RealSynarix/Cobalt-X-Zero/docs/media/images/reference/2.jpg

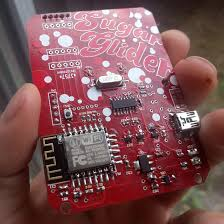
docs/media/images/reference/2.jpg
