RealSynarix/Cobalt-X-Zero/docs/media/images/reference/4.jpg

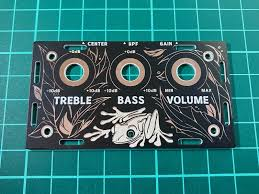
docs/media/images/reference/4.jpg
