RealSynarix/Cobalt-X-Zero/docs/media/images/reference/My-Schem.png

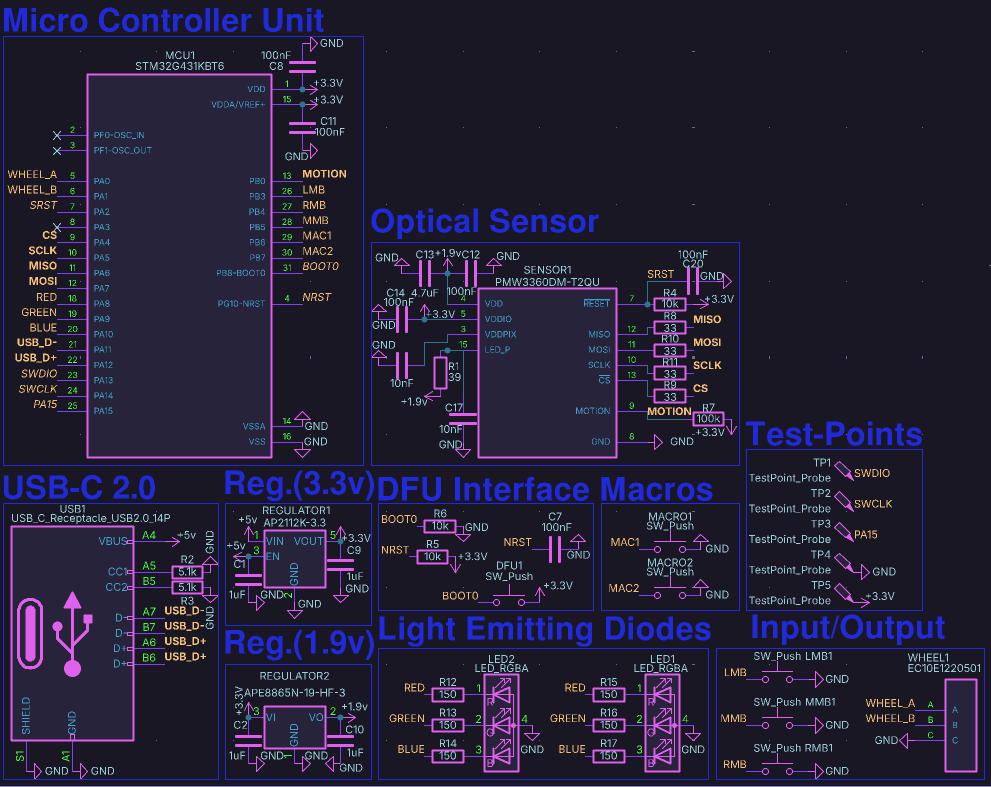
docs/media/images/reference/My-Schem.png
