RealSynarix/Cobalt-X-Zero/docs/media/images/reference/My-Sensor-Block.png

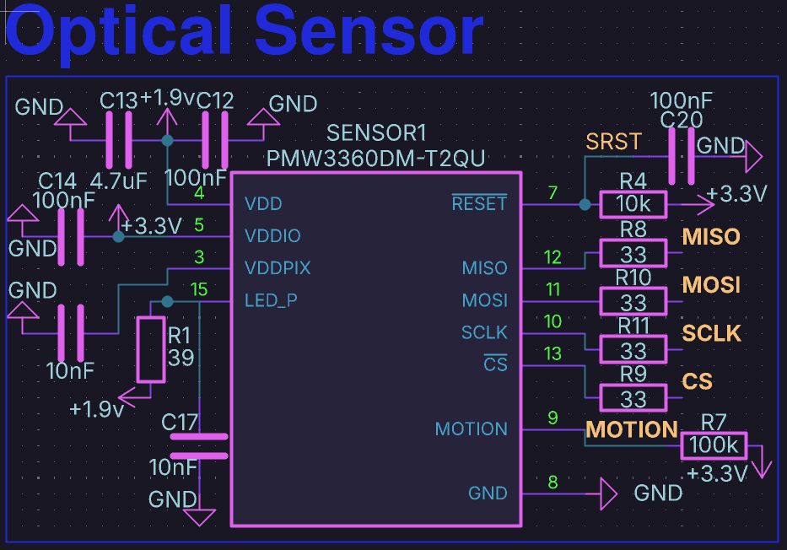
docs/media/images/reference/My-Sensor-Block.png
