RealSynarix/Cobalt-X-Zero/docs/media/images/reference/Proto1.png

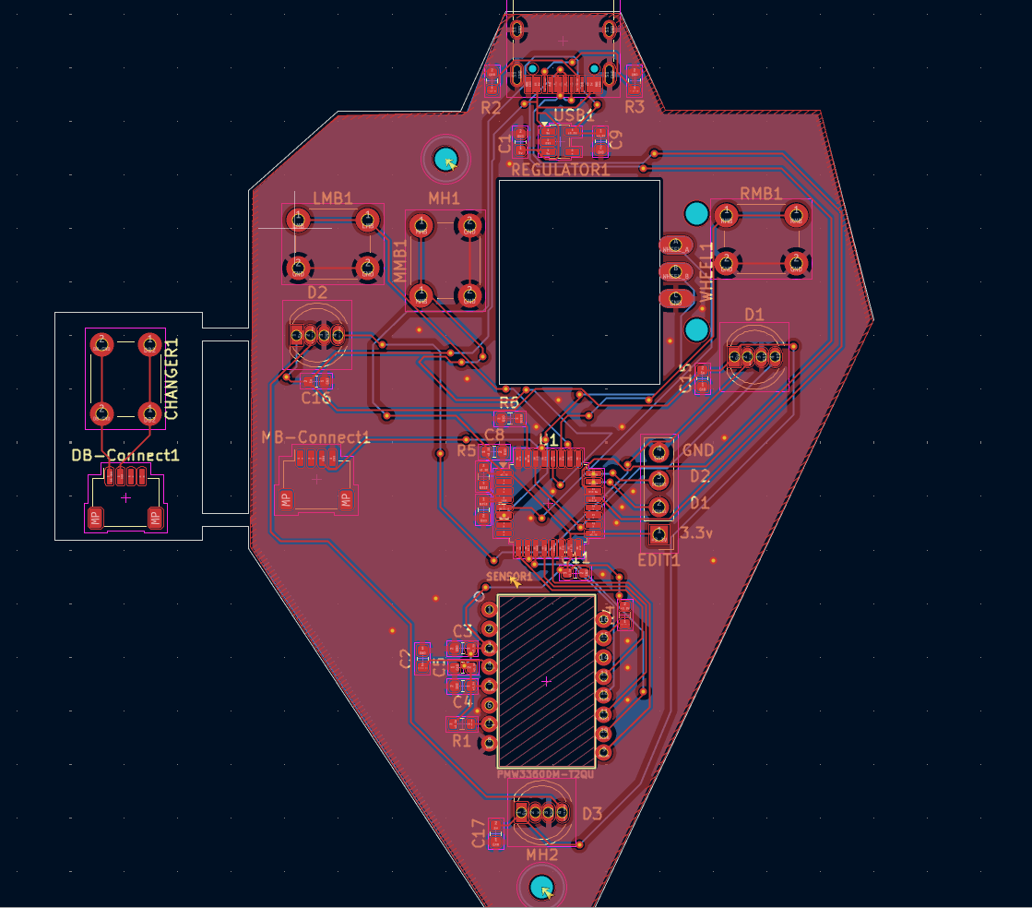
docs/media/images/reference/Proto1.png
