RealSynarix/Cobalt-X-Zero/docs/media/images/reference/Proto2-SCRAPPED.png

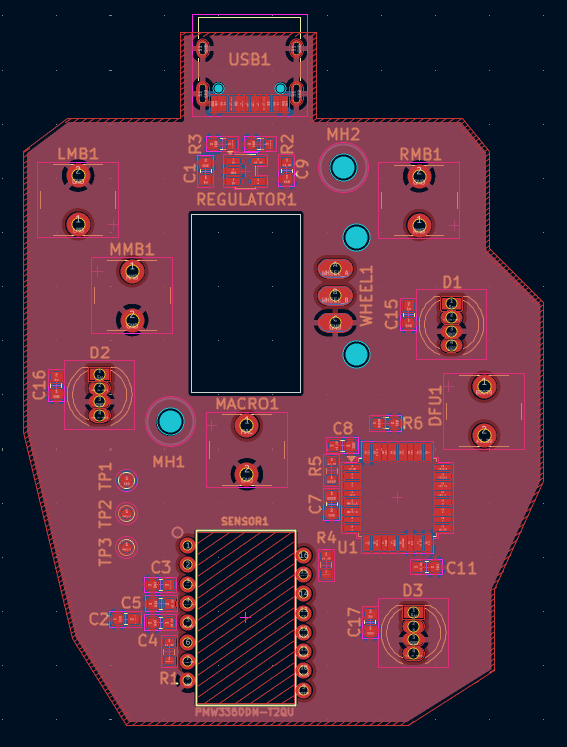
docs/media/images/reference/Proto2-SCRAPPED.png
