RealSynarix/Cobalt-X-Zero/docs/media/images/reference/working-ref.webp

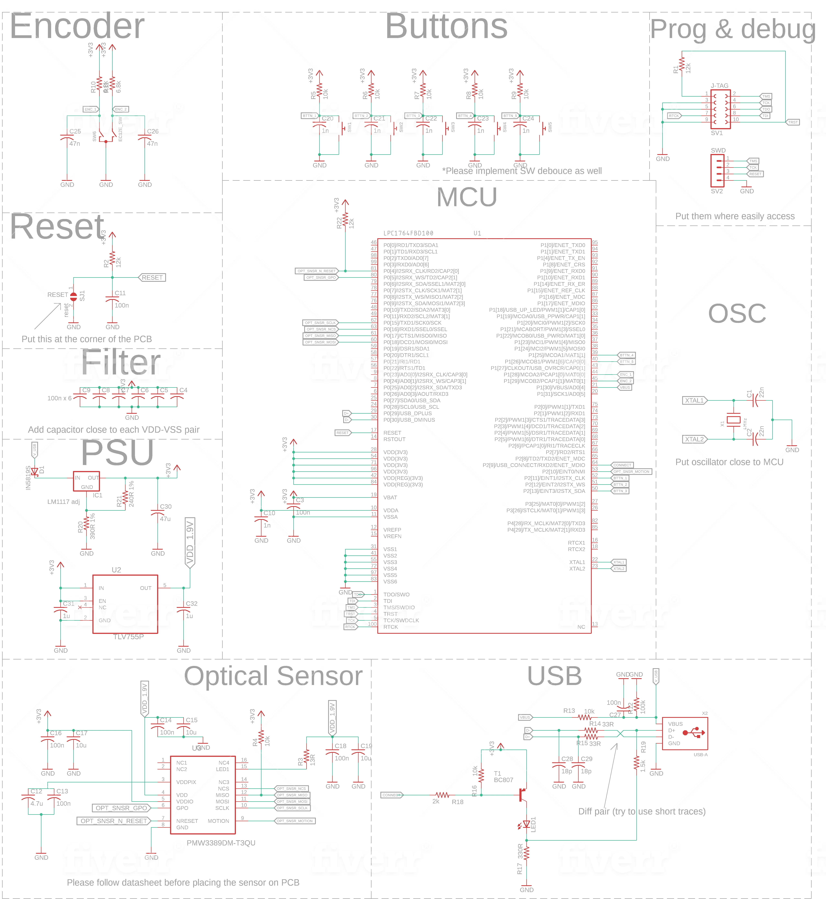
docs/media/images/reference/working-ref.webp
