RealSynarix/Cobalt-X-Zero/firmware/source/src/Sensor-Module/srom_04.h

#pragma once
#include <stdint.h>
#define SROM_04_LENGTH 4094
const uint8_t SROM_04[]={
0x01,0x04,0x8e,0x96,0x6e,0x77,0x3e,0xfe,0x7e,0x5f,0x1d,0xb8,0xf2,0x66,0x4e,0xff,
0x5d,0x19,0xb0,0xc2,0x04,0x69,0x54,0x2a,0xd6,0x2e,0xbf,0xdd,0x19,0xb0,0xc3,0xe5,
0x29,0xb1,0xe0,0x23,0xa5,0xa9,0xb1,0xc1,0x00,0x82,0x67,0x4c,0x1a,0x97,0x8d,0x79,
0x51,0x20,0xc7,0x06,0x8e,0x7c,0x7c,0x7a,0x76,0x4f,0xfd,0x59,0x30,0xe2,0x46,0x0e,
0x9e,0xbe,0xdf,0x1d,0x99,0x91,0xa0,0xa5,0xa1,0xa9,0xd0,0x22,0xc6,0xef,0x5c,0x1b,
0x95,0x89,0x90,0xa2,0xa7,0xcc,0xfb,0x55,0x28,0xb3,0xe4,0x4a,0xf7,0x6c,0x3b,0xf4,
0x6a,0x56,0x2e,0xde,0x1f,0x9d,0xb8,0xd3,0x05,0x88,0x92,0xa6,0xce,0x1e,0xbe,0xdf,
0x1d,0x99,0xb0,0xe2,0x46,0xef,0x5c,0x07,0x11,0x5d,0x98,0x0b,0x9d,0x94,0x97,0xee,
0x4e,0x45,0x33,0x6b,0x44,0xc7,0x29,0x56,0x27,0x30,0xc6,0xa7,0xd5,0xf2,0x56,0xdf,
0xb4,0x38,0x62,0xcb,0xa0,0xb6,0xe3,0x0f,0x84,0x06,0x24,0x05,0x65,0x6f,0x76,0x89,
0xb5,0x77,0x41,0x27,0x82,0x66,0x65,0x82,0xcc,0xd5,0xe6,0x20,0xd5,0x27,0x17,0xc5,
0xf8,0x03,0x23,0x7c,0x5f,0x64,0xa5,0x1d,0xc1,0xd6,0x36,0xcb,0x4c,0xd4,0xdb,0x66,
0xd7,0x8b,0xb1,0x99,0x7e,0x6f,0x4c,0x36,0x40,0x06,0xd6,0xeb,0xd7,0xa2,0xe4,0xf4,
0x95,0x51,0x5a,0x54,0x96,0xd5,0x53,0x44,0xd7,0x8c,0xe0,0xb9,0x40,0x68,0xd2,0x18,
0xe9,0xdd,0x9a,0x23,0x92,0x48,0xee,0x7f,0x43,0xaf,0xea,0x77,0x38,0x84,0x8c,0x0a,
0x72,0xaf,0x69,0xf8,0xdd,0xf1,0x24,0x83,0xa3,0xf8,0x4a,0xbf,0xf5,0x94,0x13,0xdb,
0xbb,0xd8,0xb4,0xb3,0xa0,0xfb,0x45,0x50,0x60,0x30,0x59,0x12,0x31,0x71,0xa2,0xd3,
0x13,0xe7,0xfa,0xe7,0xce,0x0f,0x63,0x15,0x0b,0x6b,0x94,0xbb,0x37,0x83,0x26,0x05,
0x9d,0xfb,0x46,0x92,0xfc,0x0a,0x15,0xd1,0x0d,0x73,0x92,0xd6,0x8c,0x1b,0x8c,0xb8,
0x55,0x8a,0xce,0xbd,0xfe,0x8e,0xfc,0xed,0x09,0x12,0x83,0x91,0x82,0x51,0x31,0x23,
0xfb,0xb4,0x0c,0x76,0xad,0x7c,0xd9,0xb4,0x4b,0xb2,0x67,0x14,0x09,0x9c,0x7f,0x0c,
0x18,0xba,0x3b,0xd6,0x8e,0x14,0x2a,0xe4,0x1b,0x52,0x9f,0x2b,0x7d,0xe1,0xfb,0x6a,
0x33,0x02,0xfa,0xac,0x5a,0xf2,0x3e,0x88,0x7e,0xae,0xd1,0xf3,0x78,0xe8,0x05,0xd1,
0xe3,0xdc,0x21,0xf6,0xe1,0x9a,0xbd,0x17,0x0e,0xd9,0x46,0x9b,0x88,0x03,0xea,0xf6,
0x66,0xbe,0x0e,0x1b,0x50,0x49,0x96,0x40,0x97,0xf1,0xf1,0xe4,0x80,0xa6,0x6e,0xe8,
0x77,0x34,0xbf,0x29,0x40,0x44,0xc2,0xff,0x4e,0x98,0xd3,0x9c,0xa3,0x32,0x2b,0x76,
0x51,0x04,0x09,0xe7,0xa9,0xd1,0xa6,0x32,0xb1,0x23,0x53,0xe2,0x47,0xab,0xd6,0xf5,
0x69,0x5c,0x3e,0x5f,0xfa,0xae,0x45,0x20,0xe5,0xd2,0x44,0xff,0x39,0x32,0x6d,0xfd,
0x27,0x57,0x5c,0xfd,0xf0,0xde,0xc1,0xb5,0x99,0xe5,0xf5,0x1c,0x77,0x01,0x75,0xc5,
0x6d,0x58,0x92,0xf2,0xb2,0x47,0x00,0x01,0x26,0x96,0x7a,0x30,0xff,0xb7,0xf0,0xef,
0x77,0xc1,0x8a,0x5d,0xdc,0xc0,0xd1,0x29,0x30,0x1e,0x77,0x38,0x7a,0x94,0xf1,0xb8,
0x7a,0x7e,0xef,0xa4,0xd1,0xac,0x31,0x4a,0xf2,0x5d,0x64,0x3d,0xb2,0xe2,0xf0,0x08,
0x99,0xfc,0x70,0xee,0x24,0xa7,0x7e,0xee,0x1e,0x20,0x69,0x7d,0x44,0xbf,0x87,0x42,
0xdf,0x88,0x3b,0x0c,0xda,0x42,0xc9,0x04,0xf9,0x45,0x50,0xfc,0x83,0x8f,0x11,0x6a,
0x72,0xbc,0x99,0x95,0xf0,0xac,0x3d,0xa7,0x3b,0xcd,0x1c,0xe2,0x88,0x79,0x37,0x11,
0x5f,0x39,0x89,0x95,0x0a,0x16,0x84,0x7a,0xf6,0x8a,0xa4,0x28,0xe4,0xed,0x83,0x80,
0x3b,0xb1,0x23,0xa5,0x03,0x10,0xf4,0x66,0xea,0xbb,0x0c,0x0f,0xc5,0xec,0x6c,0x69,
0xc5,0xd3,0x24,0xab,0xd4,0x2a,0xb7,0x99,0x88,0x76,0x08,0xa0,0xa8,0x95,0x7c,0xd8,
0x38,0x6d,0xcd,0x59,0x02,0x51,0x4b,0xf1,0xb5,0x2b,0x50,0xe3,0xb6,0xbd,0xd0,0x72,
0xcf,0x9e,0xfd,0x6e,0xbb,0x44,0xc8,0x24,0x8a,0x77,0x18,0x8a,0x13,0x06,0xef,0x97,
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
};
