RealSynarix/Cobalt-X-Zero/firmware/source/src/MCU-Module/clock.cpp

#include "clock.h"
#include <stm32g4xx_hal.h>
void clock_init(void){
__HAL_RCC_PWR_CLK_ENABLE();
HAL_PWREx_ControlVoltageScaling(PWR_REGULATOR_VOLTAGE_SCALE1_BOOST);
RCC_OscInitTypeDef o={};
o.OscillatorType=RCC_OSCILLATORTYPE_HSI|RCC_OSCILLATORTYPE_HSI48;
o.HSIState=RCC_HSI_ON;
o.HSICalibrationValue=RCC_HSICALIBRATION_DEFAULT;
o.HSI48State=RCC_HSI48_ON;
o.PLL.PLLState=RCC_PLL_ON;
o.PLL.PLLSource=RCC_PLLSOURCE_HSI;
o.PLL.PLLM=RCC_PLLM_DIV4;
o.PLL.PLLN=85;
o.PLL.PLLP=RCC_PLLP_DIV2;
o.PLL.PLLQ=RCC_PLLQ_DIV2;
o.PLL.PLLR=RCC_PLLR_DIV2;
HAL_RCC_OscConfig(&o);
while(__HAL_RCC_GET_FLAG(RCC_FLAG_HSI48RDY)==RESET){}
RCC_ClkInitTypeDef c={};
c.ClockType=RCC_CLOCKTYPE_HCLK|RCC_CLOCKTYPE_SYSCLK|RCC_CLOCKTYPE_PCLK1|RCC_CLOCKTYPE_PCLK2;
c.SYSCLKSource=RCC_SYSCLKSOURCE_PLLCLK;
c.AHBCLKDivider=RCC_SYSCLK_DIV1;
c.APB1CLKDivider=RCC_HCLK_DIV1;
c.APB2CLKDivider=RCC_HCLK_DIV1;
HAL_RCC_ClockConfig(&c,FLASH_LATENCY_4);
RCC_PeriphCLKInitTypeDef p={};
p.PeriphClockSelection=RCC_PERIPHCLK_USB;
p.UsbClockSelection=RCC_USBCLKSOURCE_HSI48;
HAL_RCCEx_PeriphCLKConfig(&p);
__HAL_RCC_CRS_CLK_ENABLE();
RCC_CRSInitTypeDef r={};
r.Prescaler=RCC_CRS_SYNC_DIV1;
r.Source=RCC_CRS_SYNC_SOURCE_USB;
r.ReloadValue=__HAL_RCC_CRS_RELOADVALUE_CALCULATE(48000000,1000);
r.ErrorLimitValue=34;
r.HSI48CalibrationValue=32;
HAL_RCCEx_CRSConfig(&r);
SystemCoreClockUpdate();
CoreDebug->DEMCR|=CoreDebug_DEMCR_TRCENA_Msk;
DWT->CYCCNT=0;
DWT->CTRL|=DWT_CTRL_CYCCNTENA_Msk;
}
