RealSynarix/Cobalt-X-Zero/Firmware/Sensor-Module/system.cpp

#include "system.h"
#include <stm32g4xx_hal.h>

void SystemClock_Config(void) {
  __HAL_RCC_PWR_CLK_ENABLE();
  HAL_PWREx_ControlVoltageScaling(PWR_REGULATOR_VOLTAGE_SCALE1_BOOST);

  RCC_OscInitTypeDef osc = { 0 };
  osc.OscillatorType = RCC_OSCILLATORTYPE_HSI | RCC_OSCILLATORTYPE_HSI48;
  osc.HSIState = RCC_HSI_ON;
  osc.HSICalibrationValue = RCC_HSICALIBRATION_DEFAULT;
  osc.HSI48State = RCC_HSI48_ON;
  osc.PLL.PLLState = RCC_PLL_ON;
  osc.PLL.PLLSource = RCC_PLLSOURCE_HSI;
  osc.PLL.PLLM = RCC_PLLM_DIV4;
  osc.PLL.PLLN = 85;
  osc.PLL.PLLP = RCC_PLLP_DIV2;
  osc.PLL.PLLQ = RCC_PLLQ_DIV2;
  osc.PLL.PLLR = RCC_PLLR_DIV2;
  HAL_RCC_OscConfig(&osc);

  while (__HAL_RCC_GET_FLAG(RCC_FLAG_HSI48RDY) == RESET)
    ;

  RCC_ClkInitTypeDef clk = { 0 };
  clk.ClockType = RCC_CLOCKTYPE_HCLK | RCC_CLOCKTYPE_SYSCLK | RCC_CLOCKTYPE_PCLK1 | RCC_CLOCKTYPE_PCLK2;
  clk.SYSCLKSource = RCC_SYSCLKSOURCE_PLLCLK;
  clk.AHBCLKDivider = RCC_SYSCLK_DIV1;
  clk.APB1CLKDivider = RCC_HCLK_DIV1;
  clk.APB2CLKDivider = RCC_HCLK_DIV1;
  HAL_RCC_ClockConfig(&clk, FLASH_LATENCY_4);

  RCC_PeriphCLKInitTypeDef periph = { 0 };
  periph.PeriphClockSelection = RCC_PERIPHCLK_USB;
  periph.UsbClockSelection = RCC_USBCLKSOURCE_HSI48;
  HAL_RCCEx_PeriphCLKConfig(&periph);

  __HAL_RCC_CRS_CLK_ENABLE();
  RCC_CRSInitTypeDef crs = { 0 };
  crs.Prescaler = RCC_CRS_SYNC_DIV1;
  crs.Source = RCC_CRS_SYNC_SOURCE_USB;
  crs.ReloadValue = __HAL_RCC_CRS_RELOADVALUE_CALCULATE(48000000, 1000);
  crs.ErrorLimitValue = 34;
  crs.HSI48CalibrationValue = 32;
  HAL_RCCEx_CRSConfig(&crs);
}
